Lewak/Turret/Schemas/audio_scheme.jpg

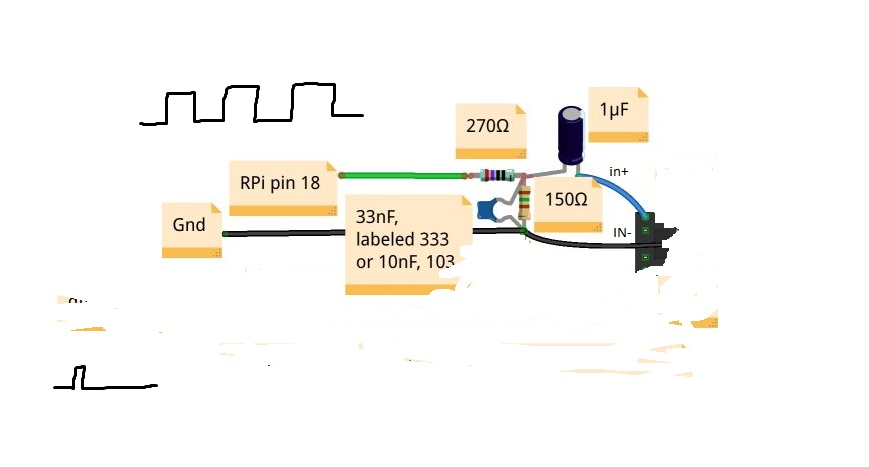
Schemas/audio_scheme.jpg
