Lewak/Turret/Schemas/Big_face.png

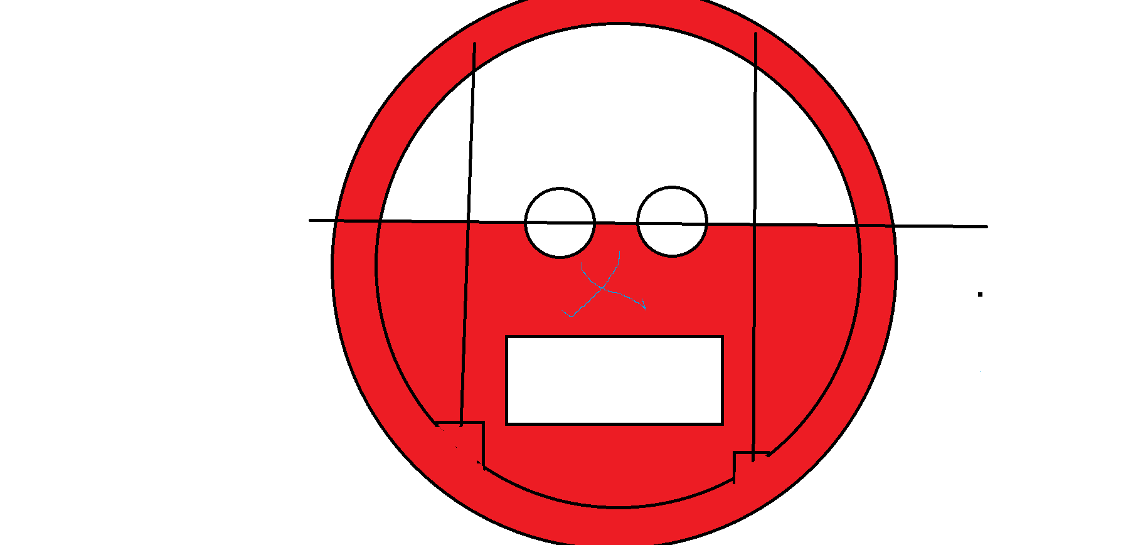
Schemas/Big_face.png
