Lewak/Turret/Schemas/Błąd Kardynalny.png

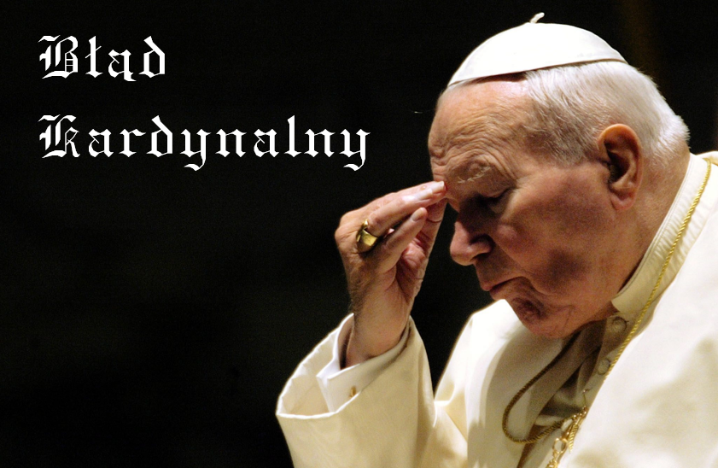
Schemas/Błąd Kardynalny.png
