Lewak/Turret/Schemas/main mechanism v0.png

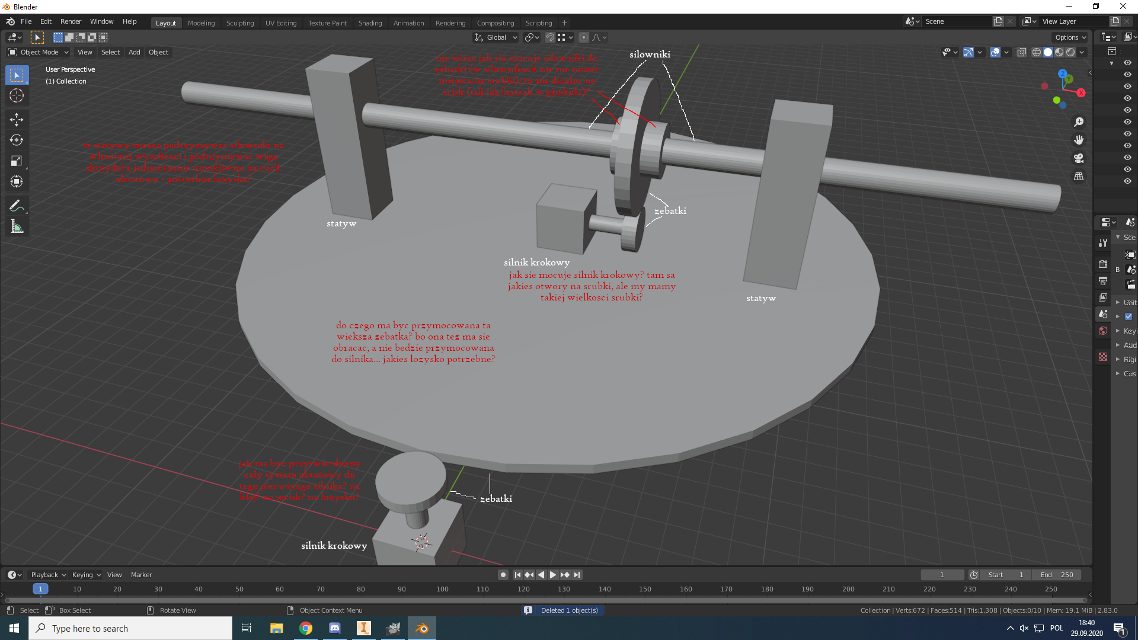
Schemas/main mechanism v0.png
