Lewak/Turret/LogicRaspberry/main.py

import atexit
from peripherals import Peripherals
from state_machine import StateMachine
from sleep_state import SleepState


try:
    Peripherals.initialise()
    print("Attention evacuation emergency all personnel must evacuate immediately")
    stateMachine = StateMachine()
    stateMachine.set_initial_state(SleepState())
    stateMachine.run()
except Exception as e:
    print("An error occurred:", e)
except KeyboardInterrupt:
    print("key")
    pass
finally:
    Peripherals.destroy()
    print("Shutdown complete")
