Lewak/Turret/LogicRaspberry/servo.py

from gpio_interface import GpioInterface


class Servo:
    _minPosition = 500
    _maxPosition = 2500

    def __init__(self, pin: int):
        self.pin = pin

    def setAngle(self, angleDegrees: float) -> None:
        position = angleDegrees*(Servo._maxPosition - Servo._minPosition)/180 + Servo._minPosition
        position = min(position, Servo._maxPosition)
        position = max(position, Servo._minPosition)
        GpioInterface.setServoPosition(self.pin, int(position))

    def destroy(self) -> None:
        pass
