Lewak/Turret/LogicRaspberry/laser.py

from gpio_interface import GpioInterface


class Laser:
    def __init__(self, pin: int):
        self.pin = pin
        GpioInterface.setup(self.pin, GpioInterface.OUT)

    def turnOn(self) -> None:
        GpioInterface.writePin(self.pin, True)

    def turnOff(self) -> None:
        GpioInterface.writePin(self.pin, False)
